tonykoop/fujara/build/packet/validation-loop.csv

check_id | packet_artifact | readiness_before | prediction_source | target | tolerance | method | measured_result | status | next_action | evidence | source_status
BVL-001 | family-spec.csv | L2 V5 build-packet candidate | FS-001 | acoustic_law hypothesis is explicit and not mixed with production rows | all L2 gates reviewed | file review and schema check | Pending entry after explicit branch fields are reviewed | open | Add explicit family rows for side-branch acoustic model | build/packet/family-spec.csv | open
BVL-002 | bore-station-plan.csv | L2 V5 build-packet candidate | BS-001..BS-004 | At least 3 measured stations include end-condition impact variables | required values and tool ids | Measure with ruler/caliper and log tool/date | Pending | planned | Collect bore and side-branch dimensions before any bore-dimensioned drawing claims | build/packet/bore-station-plan.csv | not_measured
BVL-003 | design-table/fujara-dimensions-parametric.xlsx | L2 V5 build-packet candidate | Derived design table | Existing parametric rows remain scaffold references | No design-table-only claims for fabrication | Cross-check formula variables and branch assumptions against planned station logs | Pending | planned | Use these rows as priors only until measurements exist | design-table/fujara-dimensions-parametric.xlsx | reviewed_only
BVL-004 | visual-output-register.csv | L2 V5 build-packet candidate | VOREG-001 | Differentiate concept/reference outputs from authority candidates | No non-authority visuals in fabrication chain | Run validation-gate review and update register | Pending | open | Keep generated or concept visuals at `concept_only` until capture completes | build/packet/visual-output-register.csv | not_checked
BVL-005 | validation.csv | L2 V5 build-packet candidate | This packet | All open gates are resolved before L3 | All `open` gates clear | Update required rows and add measured evidence before promotion | Pending | open | Link each gate with evidence path and status | build/packet/validation.csv | blocked
